Inssomniak/ESP8266-Barometer/images/image-1.jpg

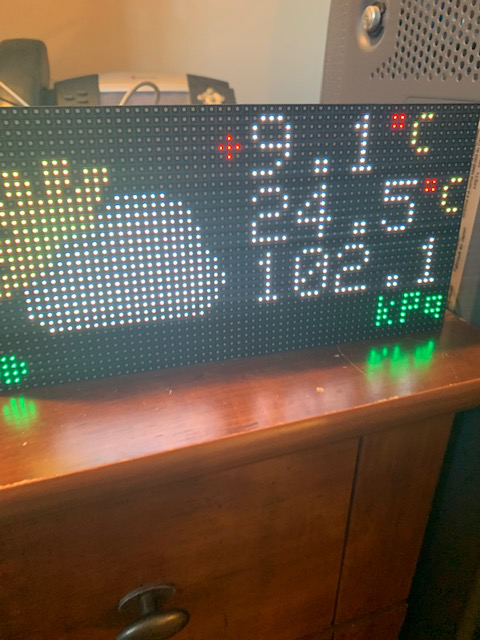
images/image-1.jpg
