Inssomniak/ESP8266-Barometer/images/image-2.jpg

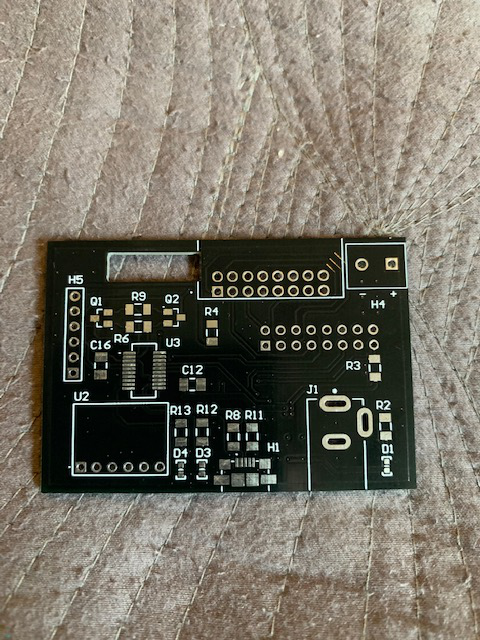
images/image-2.jpg
