Inssomniak/ESP8266-Barometer/images/image-3.jpg

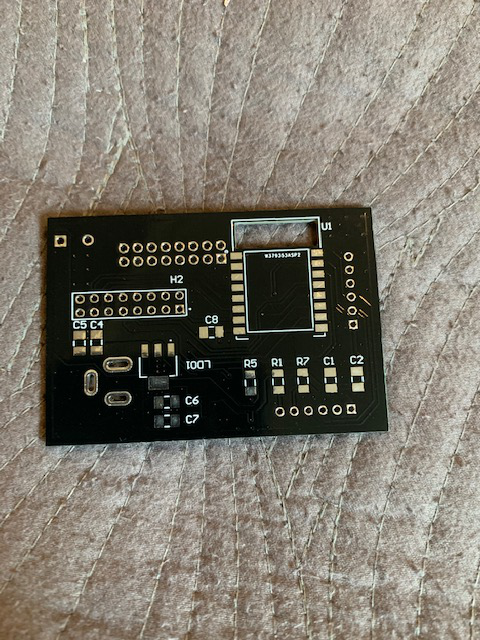
images/image-3.jpg
