Inssomniak/ESP8266-Barometer/images/image-5.jpg

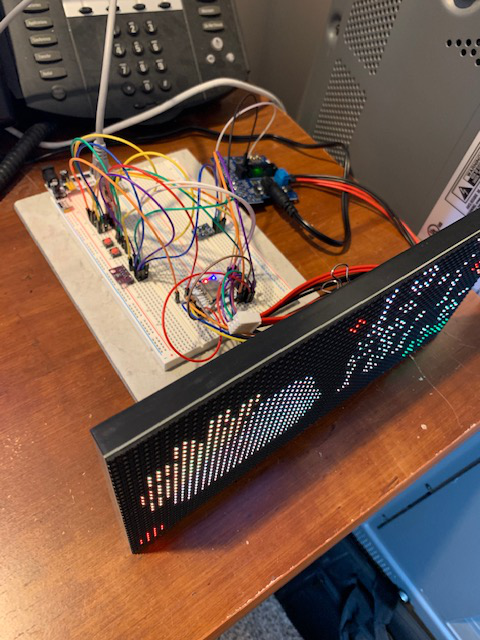
images/image-5.jpg
