Inssomniak/ESP8266-Barometer/images/IMG_0618.jpg

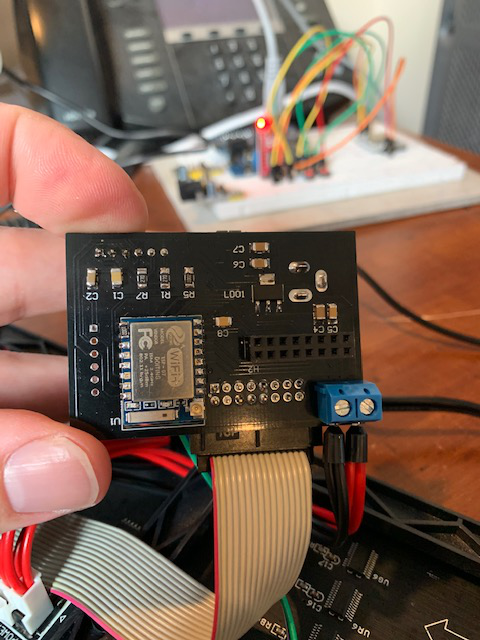
images/IMG_0618.jpg
